tanmaylad77/KDT_Hierarchical_KiBot/HTML/images/cat_pdf_drill_map_LE_BMS_A_V2-PTH_drill_map.png

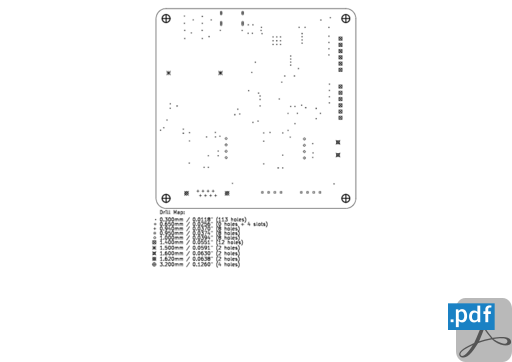
HTML/images/cat_pdf_drill_map_LE_BMS_A_V2-PTH_drill_map.png
