tanmaylad77/KDT_Hierarchical_KiBot/HTML/images/cat_png_3d_viewer_angled_bottom_LE_BMS_A_V2-angled_bottom.png

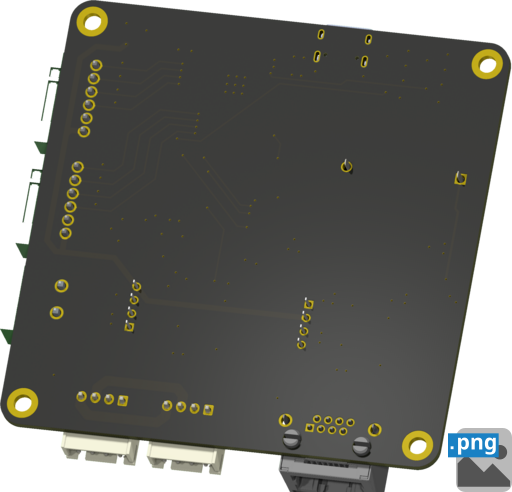
HTML/images/cat_png_3d_viewer_angled_bottom_LE_BMS_A_V2-angled_bottom.png
