tanmaylad77/KDT_Hierarchical_KiBot/Manufacturing/Fabrication/LE_BMS_A_V2-fabrication.pdf

# Top Fabrication (Scale 1:1)

# LE_BMS_A_V2 Fabrication Document

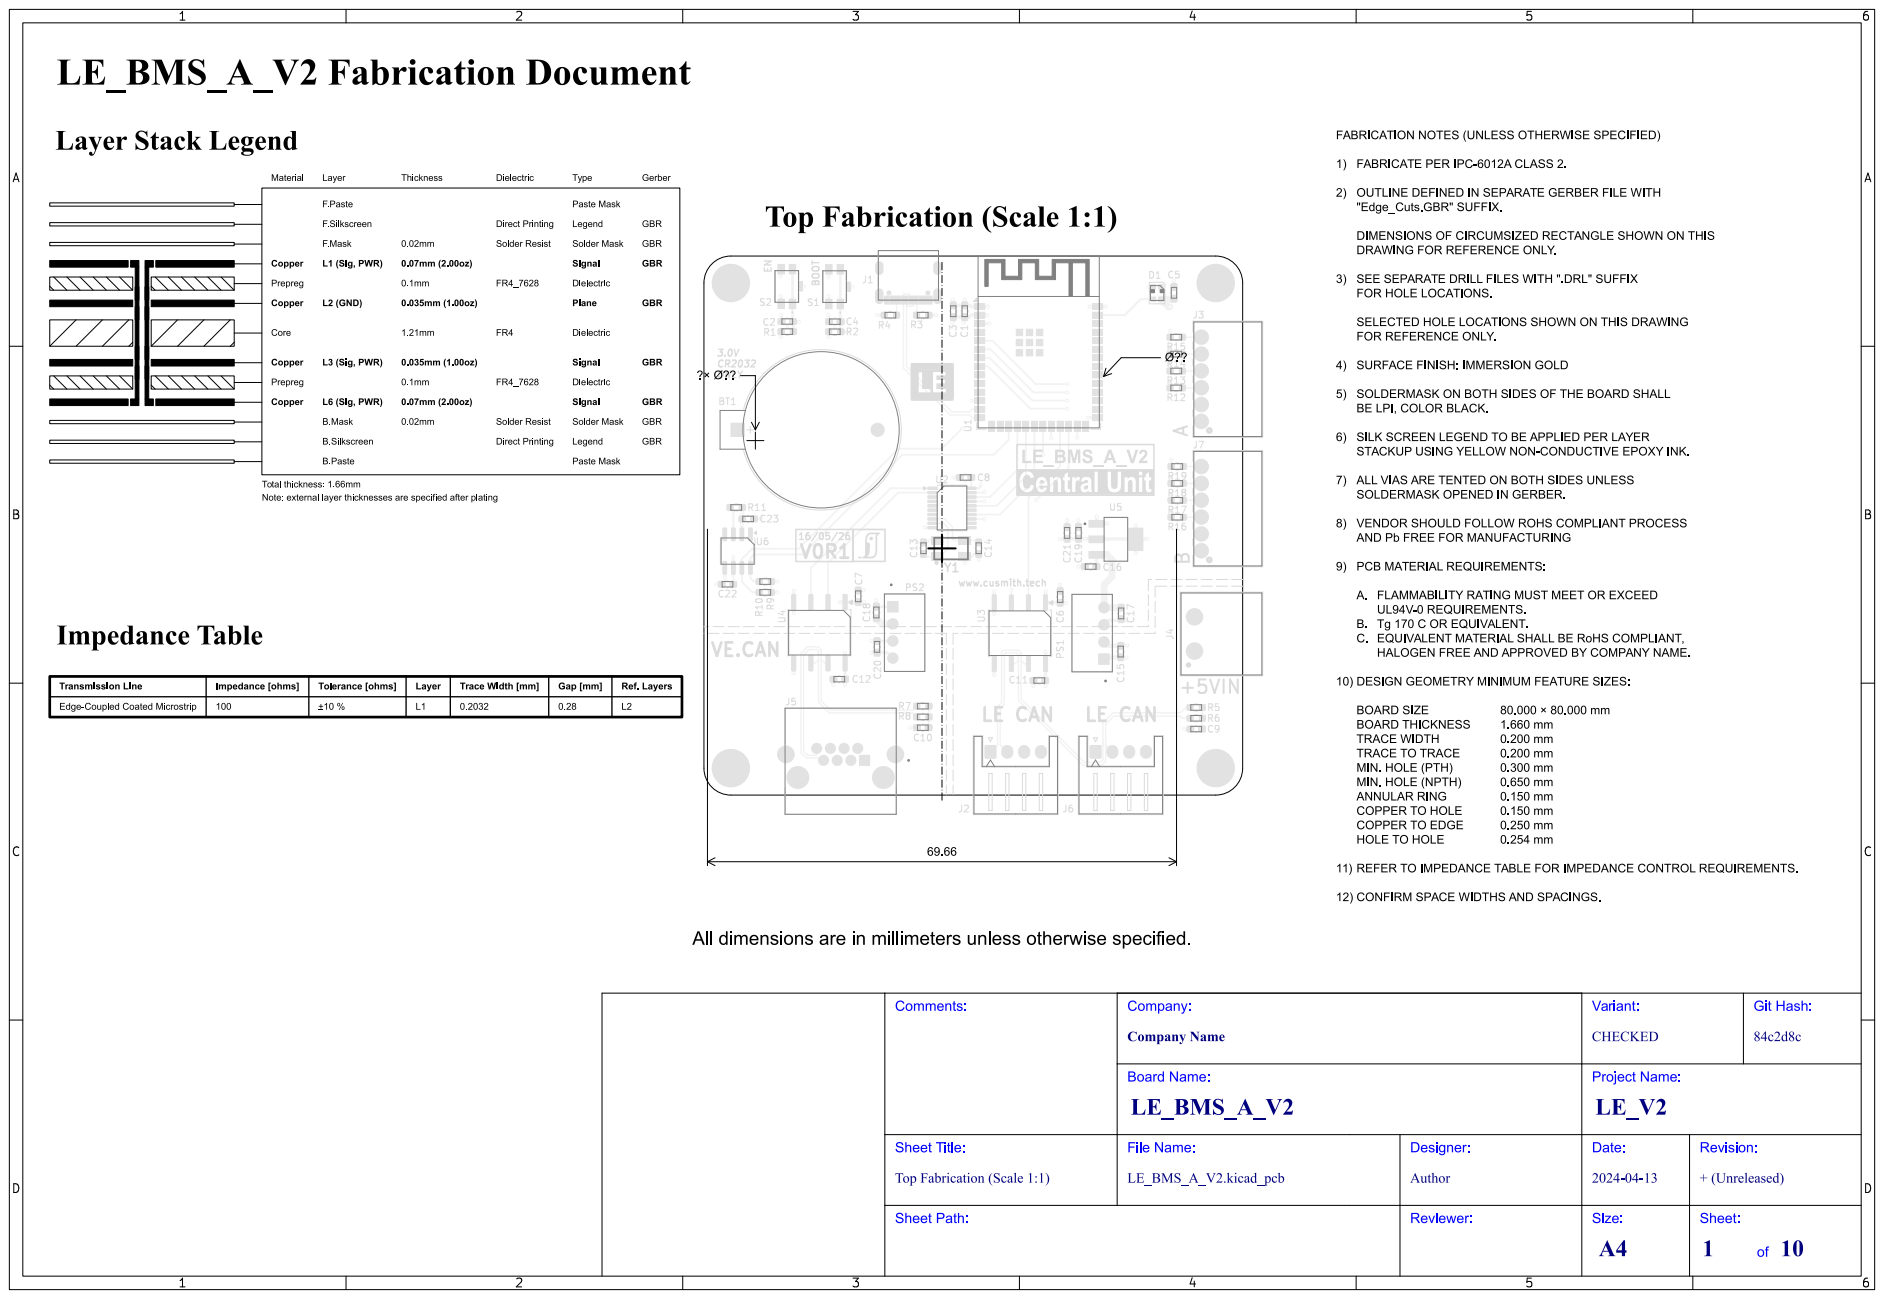
[picture p19: page 1]

# Bottom Fabrication (Scale 1:1)

# LE_BMS_A_V2 Fabrication Document

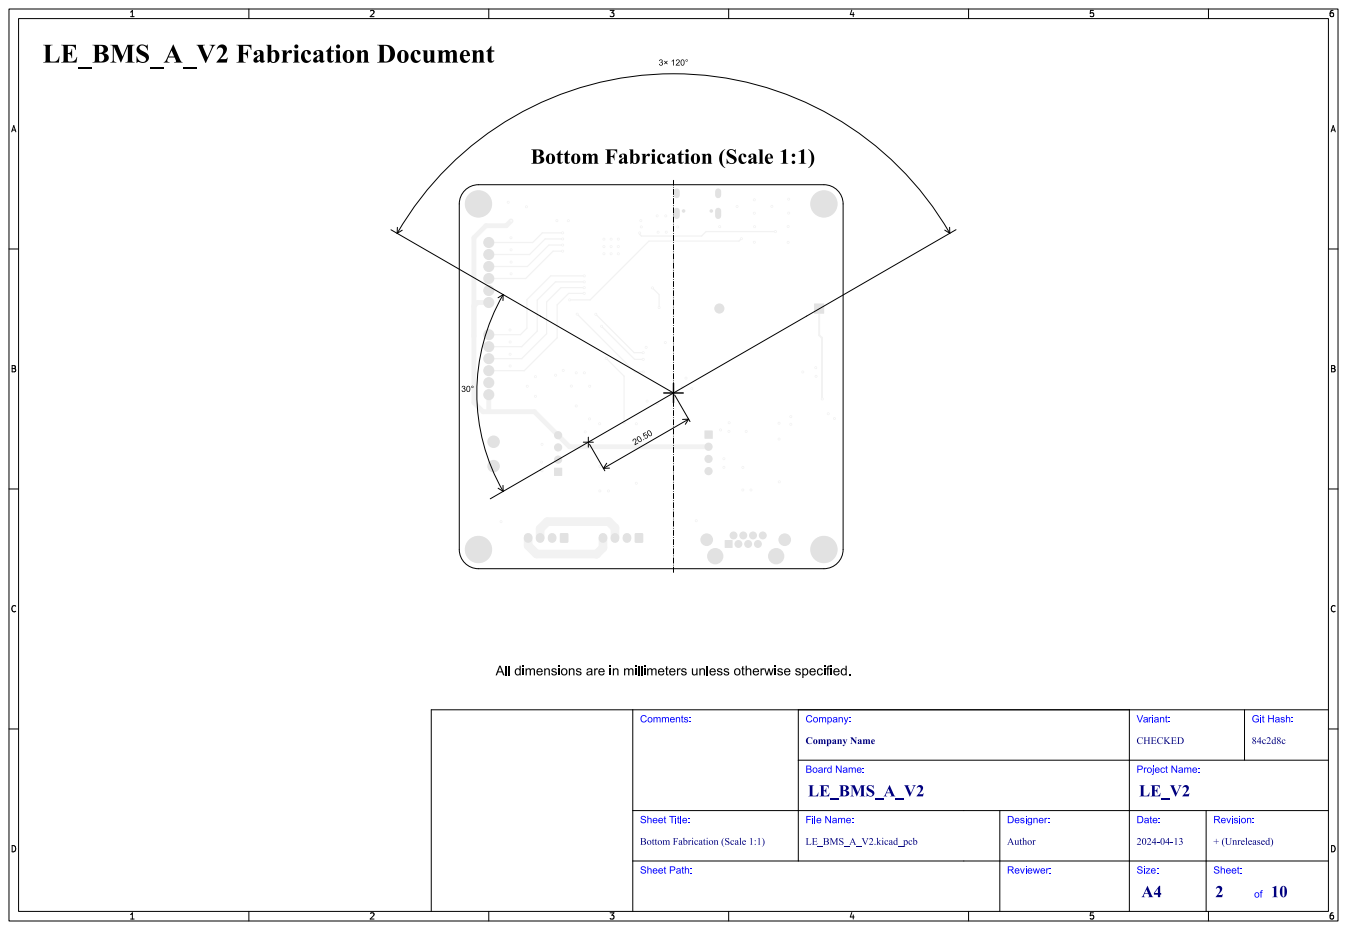
[picture p20: page 2]
Git; Hash:; Comments:; Sheet Path:; Sheet Title:; File Name:; LE_BMS_A_V2; Company Name; Company:; CHECKED; Variant:; Board Name:; LE_BMS_A_V2.kicad_pcb; Author; Designer:; Reviewer:; Project Name:; Date:; + (Unreleased); Revision:; Size:; Sheet:

Bottom Fabrication (Scale 1:1)

# Drill Drawing L1 - L4 (Scale 1:1)

# LE_BMS_A_V2 Fabrication Document

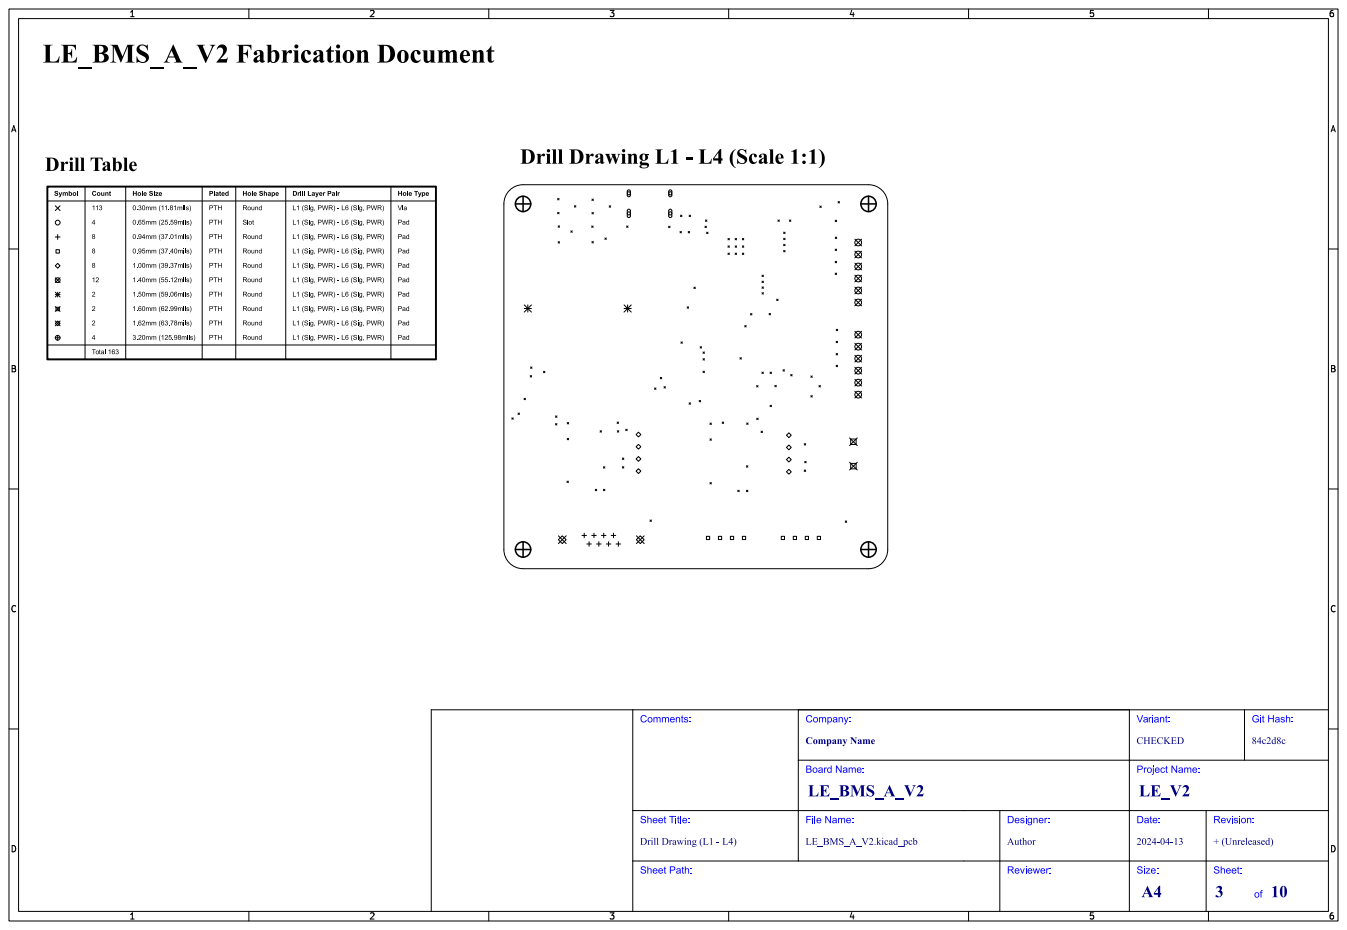
[picture p21: page 3]
Git; Hash:; Comments:; Drill Drawing (L1 - L4); Sheet Path:; Sheet Title:; File Name:; LE_BMS_A_V2; Company Name; Company:; CHECKED; Variant:; Board Name:; LE_BMS_A_V2.kicad_pcb; Author; Designer:; Reviewer:; Project Name:; Date:; + (Unreleased); Revision:; Size:; Sheet:

# Drill Drawing L1 - L4 (Scale 1:1)

# LE_BMS_A_V2 Fabrication Document

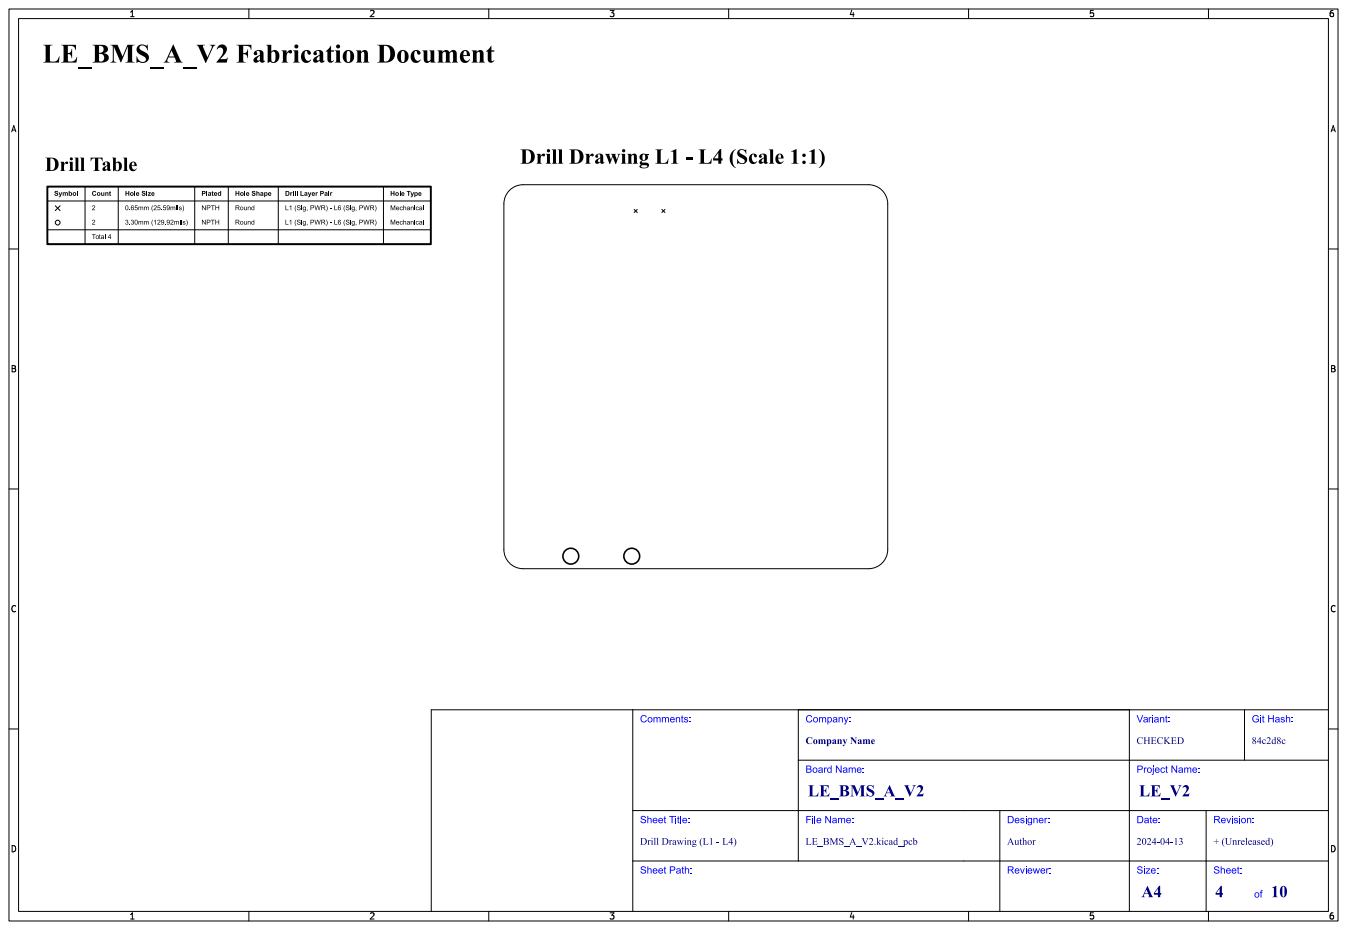
[picture p22: page 4]
Git; Hash:; Comments:; Drill Drawing (L1 - L4); Sheet Path:; Sheet Title:; File Name:; LE_BMS_A_V2; Company Name; Company:; CHECKED; Variant:; Board Name:; LE_BMS_A_V2.kicad_pcb; Author; Designer:; Reviewer:; Project Name:; Date:; + (Unreleased); Revision:; Size:; Sheet:

# Top Test Points (Scale 1:1)

# LE_BMS_A_V2 Fabrication Document

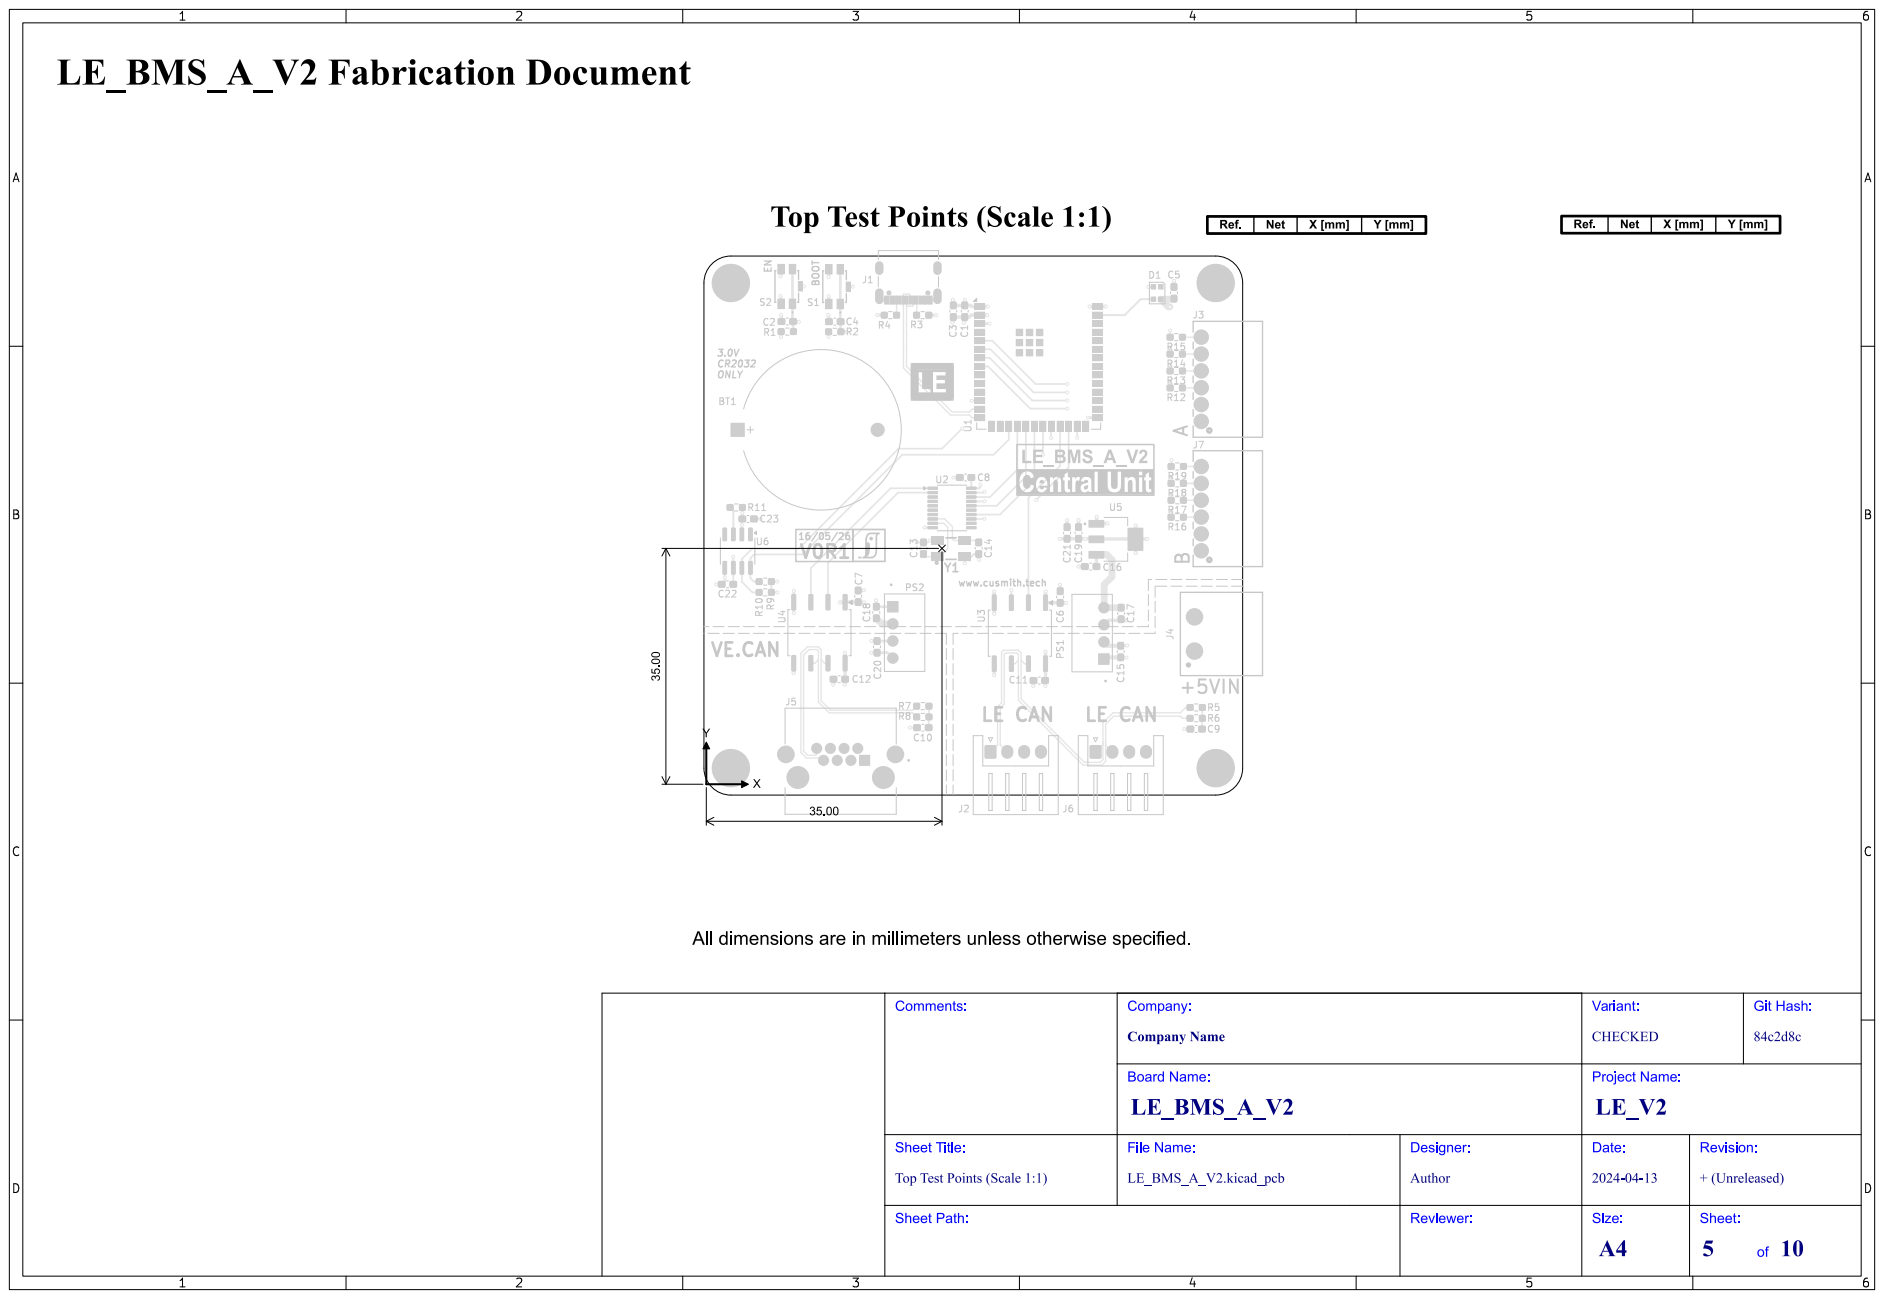
[picture p23: page 5]

Top Test Points (Scale 1:1)

# Bottom Test Points (Scale 1:1)

# LE_BMS_A_V2 Fabrication Document

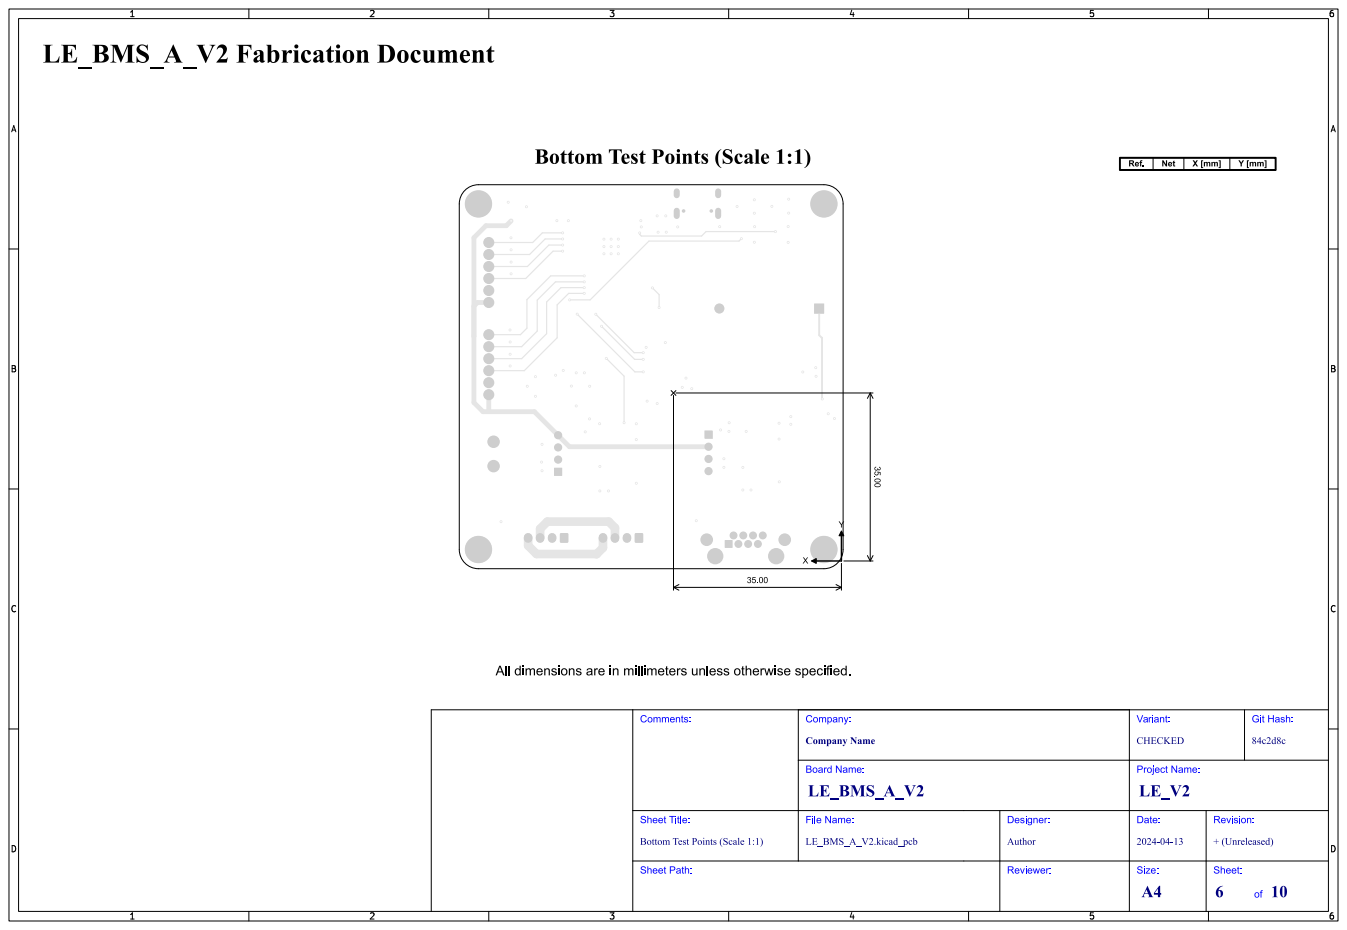
[picture p24: page 6]
Git; Hash:; Comments:; Sheet Path:; Sheet Title:; File Name:; LE_BMS_A_V2; Company Name; Company:; CHECKED; Variant:; Board Name:; LE_BMS_A_V2.kicad_pcb; Author; Designer:; Reviewer:; Project Name:; Date:; + (Unreleased); Revision:; Size:; Sheet:

Bottom Test Points (Scale 1:1)

# L1 (Sig, PWR) (Scale 1:1)

# LE_BMS_A_V2 Fabrication Document

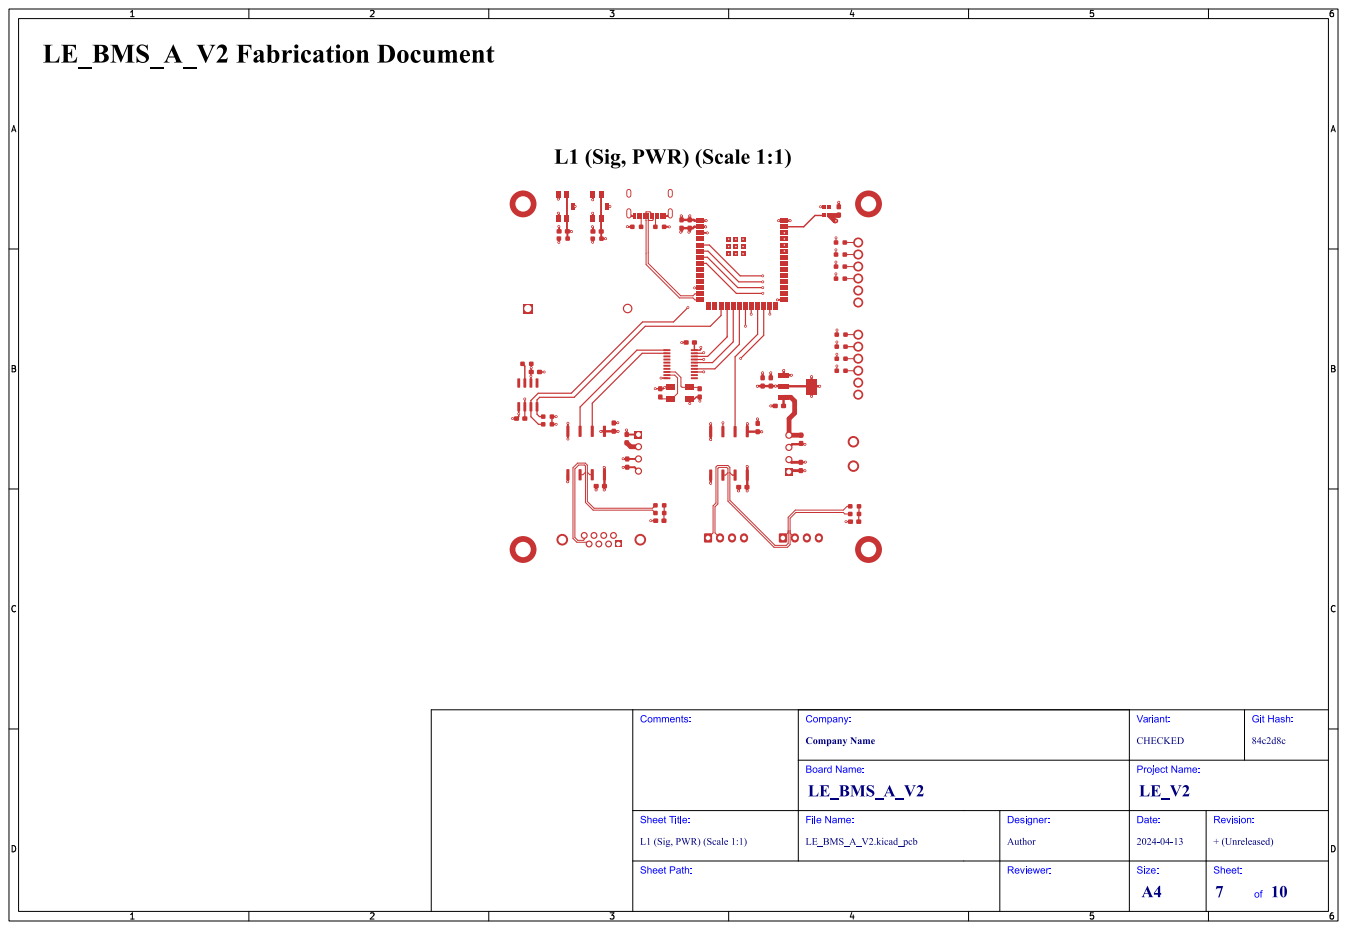
[picture p25: page 7]
Git; Hash:; Comments:; Sheet Path:; Sheet Title:; File Name:; LE_BMS_A_V2; Company Name; Company:; CHECKED; Variant:; Board Name:; LE_BMS_A_V2.kicad_pcb; Author; Designer:; Reviewer:; Project Name:; Date:; + (Unreleased); Revision:; Size:; Sheet:

L1 (Sig, PWR) (Scale 1:1)

# L2 (GND) (Scale 1:1)

# LE_BMS_A_V2 Fabrication Document

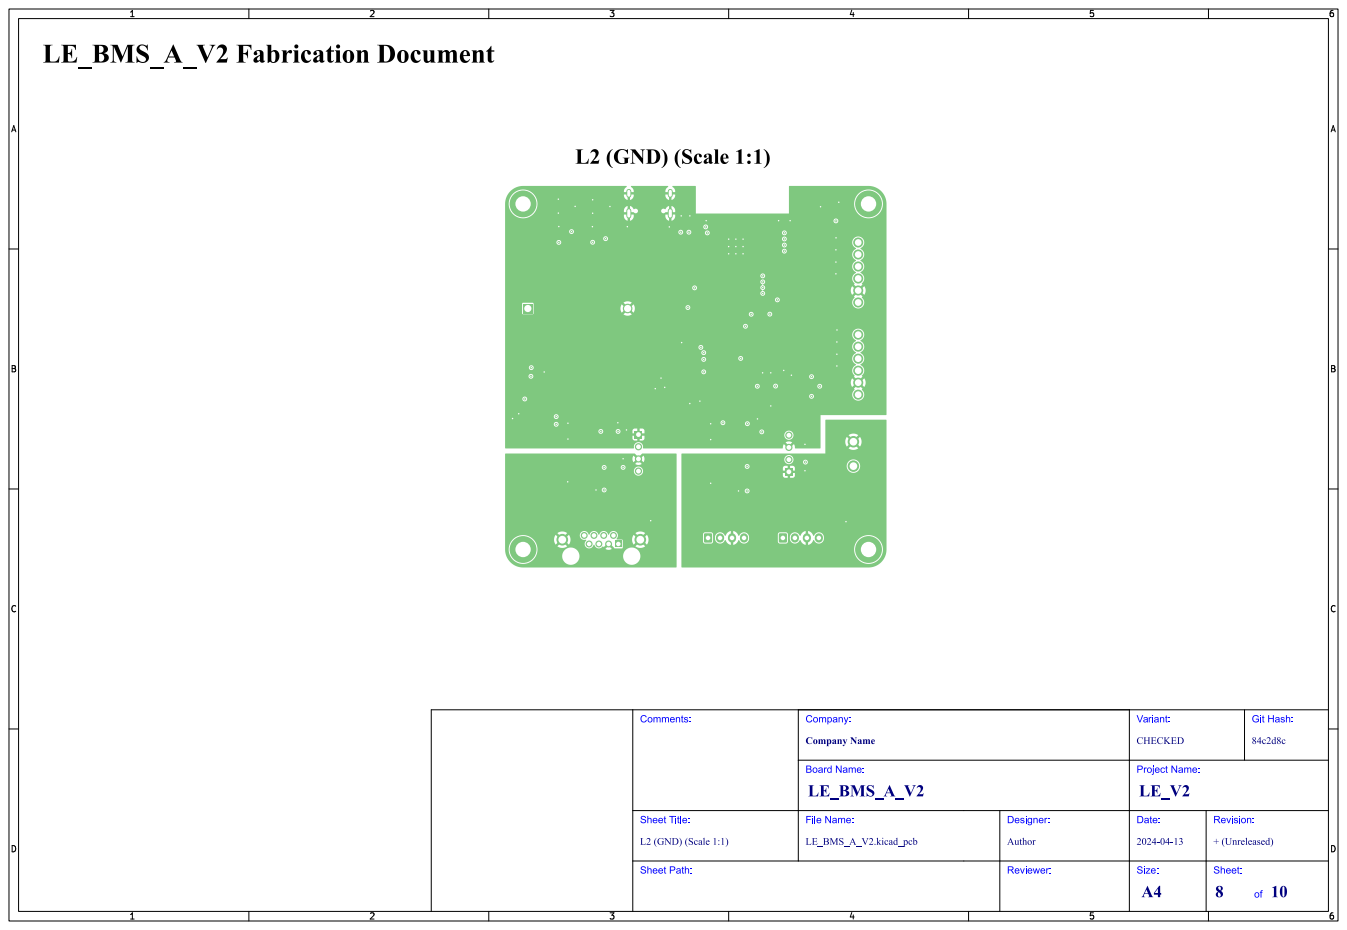
[picture p26: page 8]
Git; Hash:; Comments:; L2 (GND) (Scale 1:1); Sheet Path:; Sheet Title:; File Name:; LE_BMS_A_V2; Company Name; Company:; CHECKED; Variant:; Board Name:; LE_BMS_A_V2.kicad_pcb; Author; Designer:; Reviewer:; Project Name:; Date:; + (Unreleased); Revision:; Size:; Sheet:

# L3 (Sig, PWR) (Scale 1:1)

# LE_BMS_A_V2 Fabrication Document

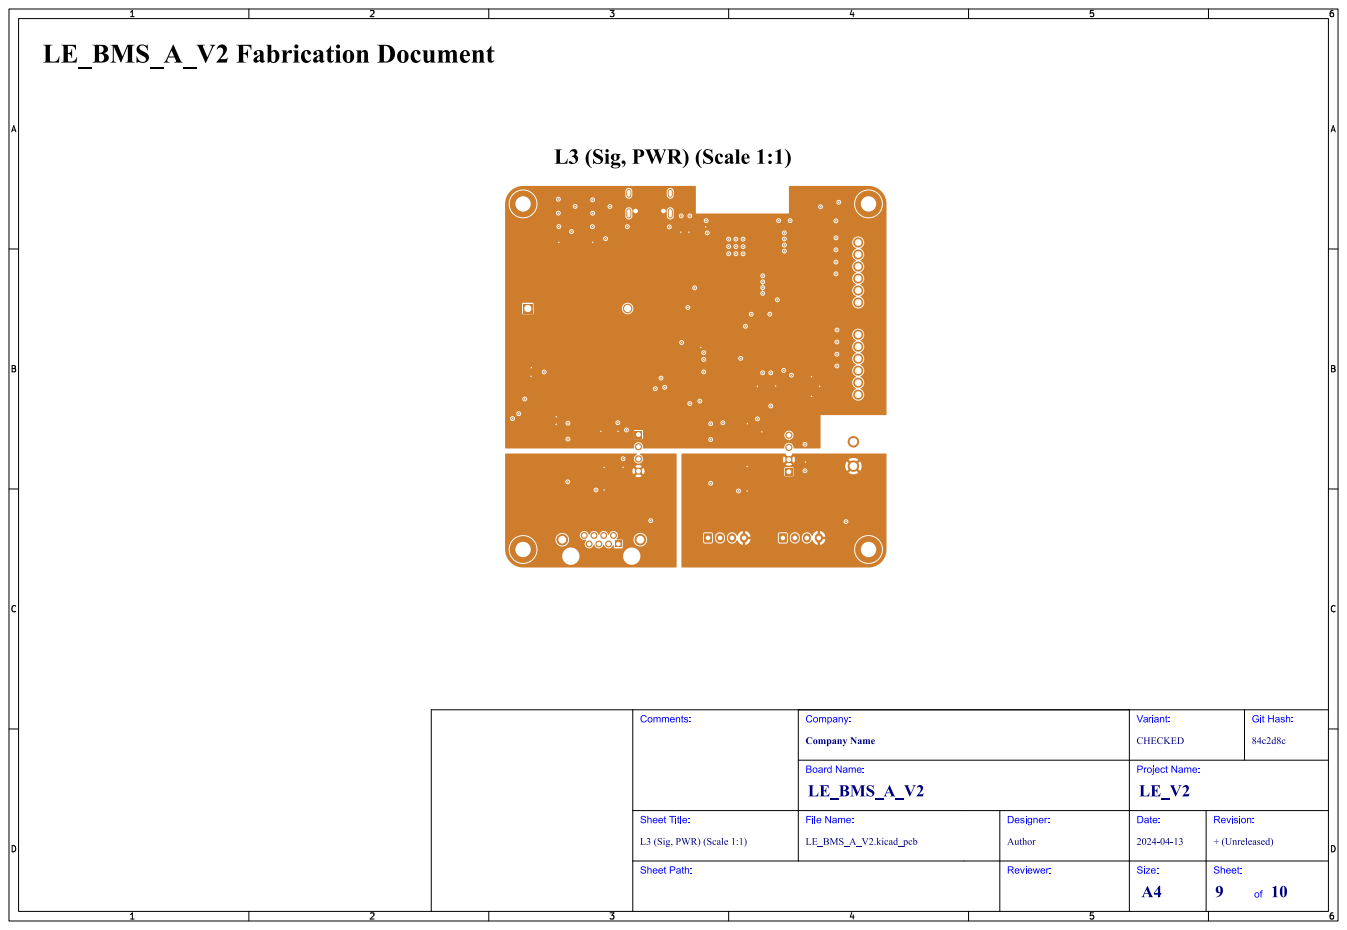
[picture p27: page 9]
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

L3 (Sig, PWR) (Scale 1:1)

# L6 (Sig, PWR) (Scale 1:1)

# LE_BMS_A_V2 Fabrication Document

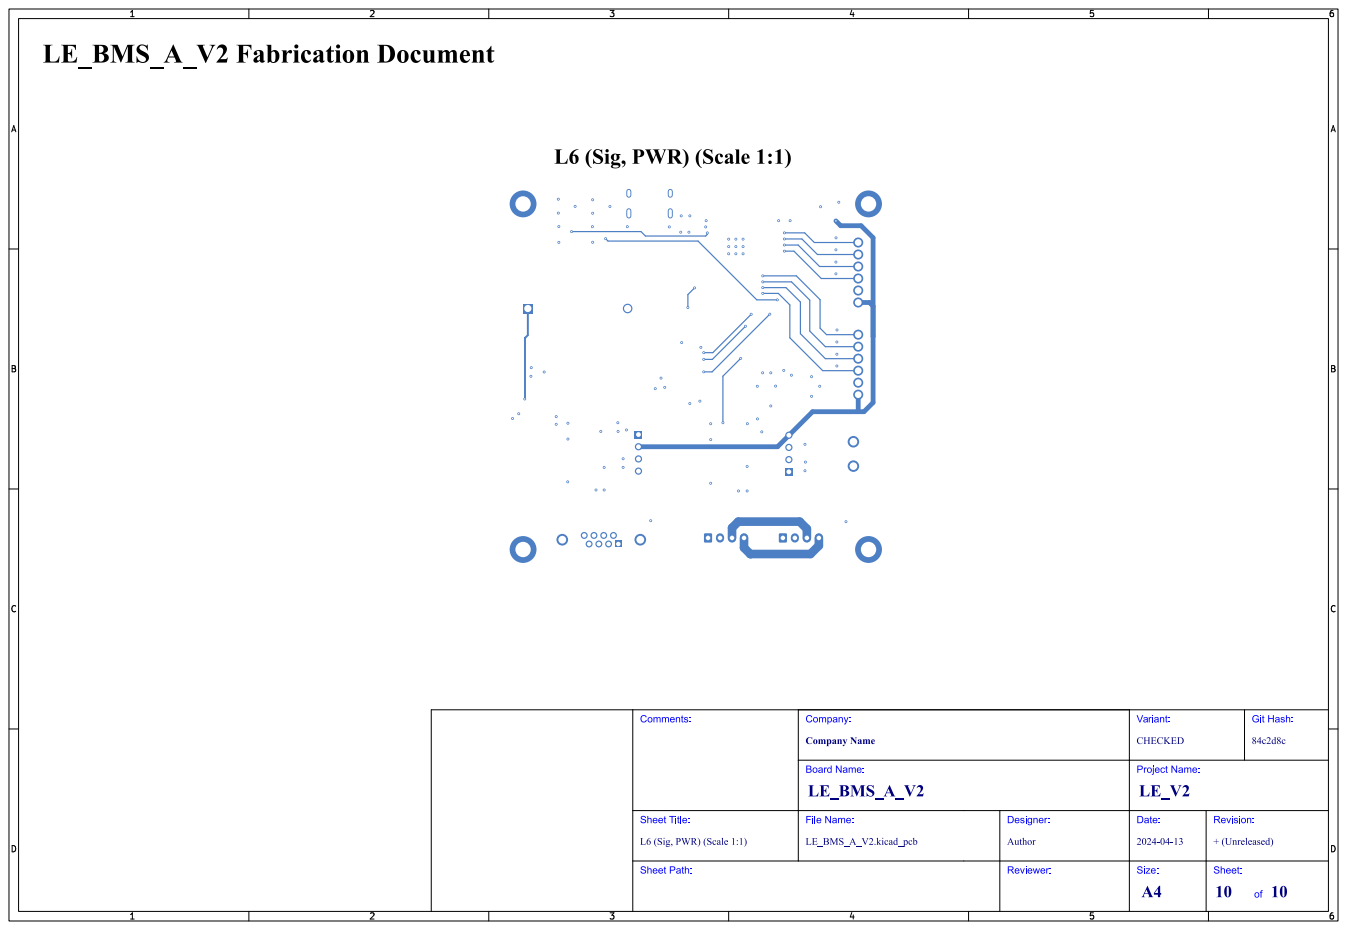
[picture p28: page 10]
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

L6 (Sig, PWR) (Scale 1:1)
