tanmaylad77/KDT_Hierarchical_KiBot/Manufacturing/Assembly/LE_BMS_A_V2-assembly-3.pdf

# Bottom Assembly (Scale 1:1)

# LE_BMS_A_V2 Assembly Document

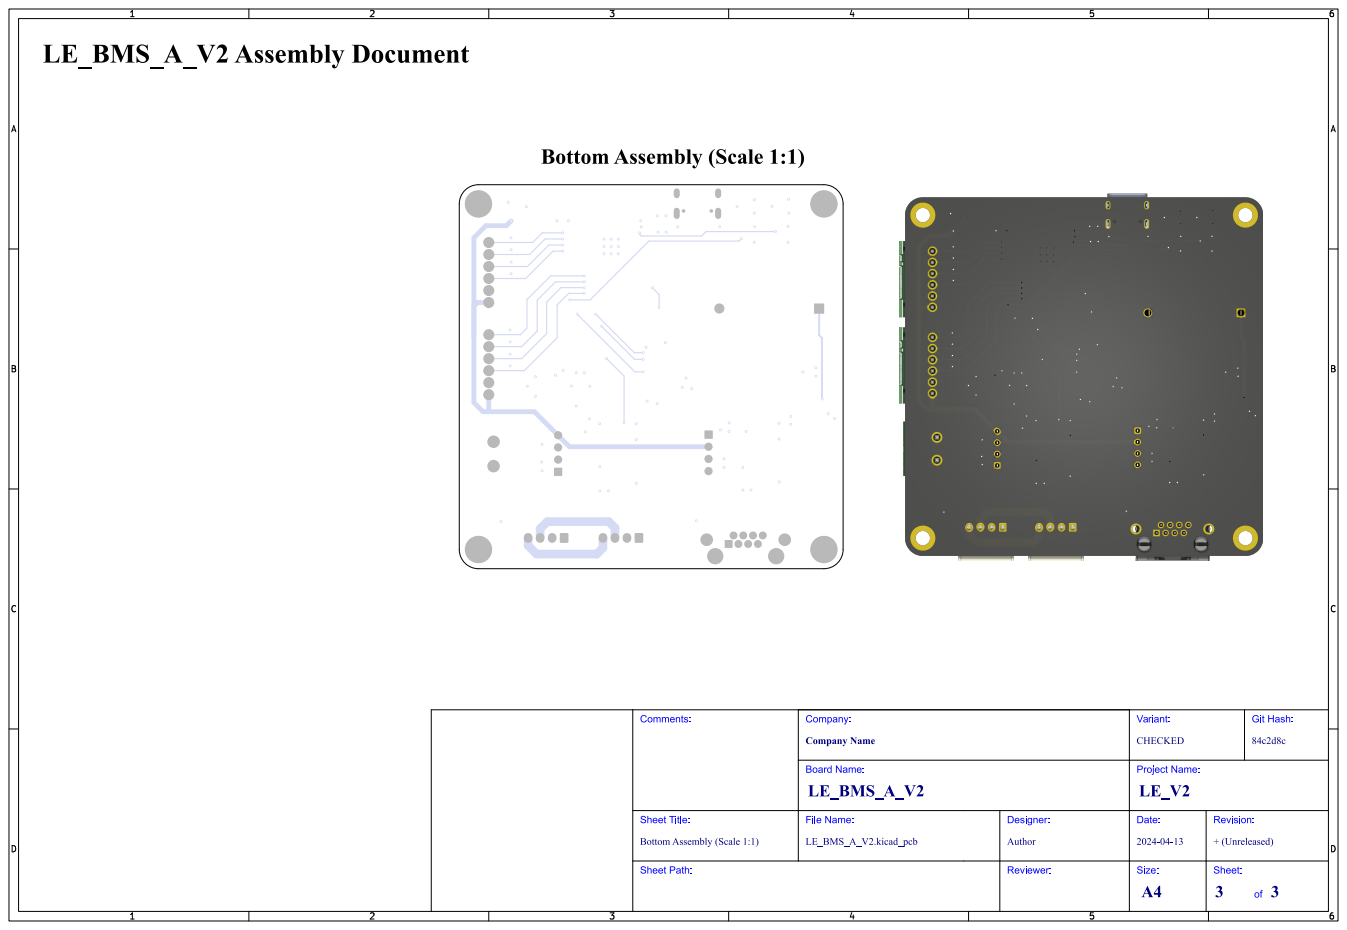
[picture p41: page 1]
Git; Hash:; Comments:; Sheet Path:; Sheet Title:; File Name:; LE_BMS_A_V2; Company Name; Company:; CHECKED; Variant:; Board Name:; LE_BMS_A_V2.kicad_pcb; Author; Designer:; Reviewer:; Project Name:; Date:; + (Unreleased); Revision:; Size:; Sheet: 3

Bottom Assembly (Scale 1:1)
