tanmaylad77/KDT_Hierarchical_KiBot/Manufacturing/Assembly/LE_BMS_A_V2-assembly.pdf

# LE_BMS_A_V2 Assembly Document

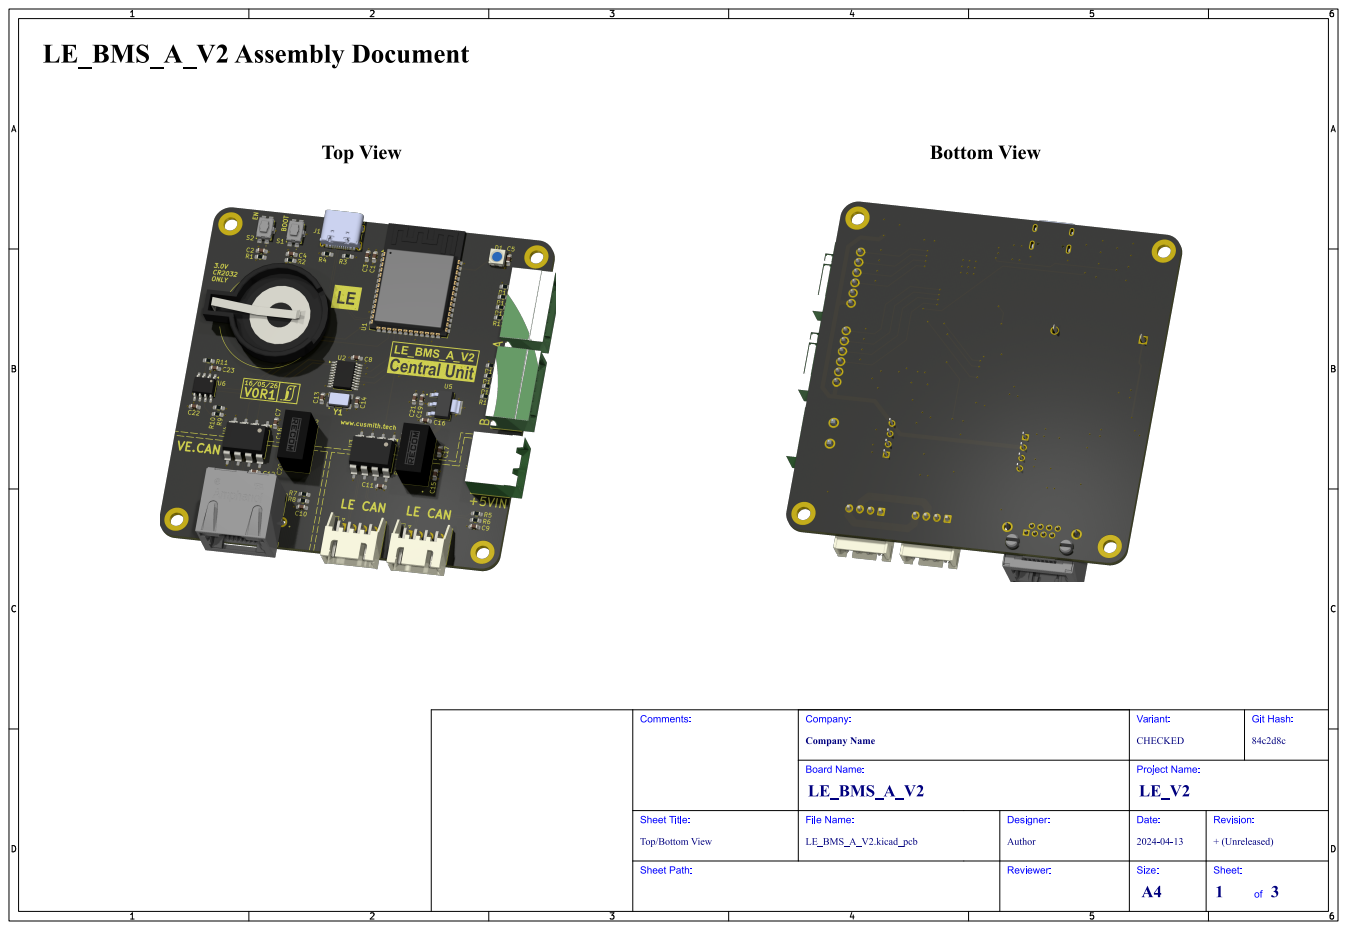
[picture p42: page 1]
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

Top/Bottom View

# Top Assembly (Scale 1:1)

# LE_BMS_A_V2 Assembly Document


# Bottom Assembly (Scale 1:1)

# LE_BMS_A_V2 Assembly Document

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

Bottom Assembly (Scale 1:1)
