tanmaylad77/KDT_Hierarchical_KiBot/Manufacturing/Fabrication/LE_BMS_A_V2-fabrication-10.pdf

# L6 (Sig, PWR) (Scale 1:1)

# LE_BMS_A_V2 Fabrication Document

Git; Hash:; Comments:; Sheet Path:; Sheet Title:; File Name:; LE_BMS_A_V2; Company Name; Company:; CHECKED; Variant:; Board Name:; LE_BMS_A_V2.kicad_pcb; Author; Designer:; Reviewer:; Project Name:; Date:; + (Unreleased); Revision:; Size:; Sheet: 10

L6 (Sig, PWR) (Scale 1:1)
