tanmaylad77/KDT_Hierarchical_KiBot/Manufacturing/Fabrication/LE_BMS_A_V2-fabrication-1.pdf

# Top Fabrication (Scale 1:1)

# LE_BMS_A_V2 Fabrication Document
