tanmaylad77/KDT_Hierarchical_KiBot/Manufacturing/Fabrication/LE_BMS_A_V2-fabrication-5.pdf

# Top Test Points (Scale 1:1)

# LE_BMS_A_V2 Fabrication Document


Top Test Points (Scale 1:1)
