tanmaylad77/KDT_Hierarchical_KiBot/Manufacturing/Fabrication/Gerbers/LE_BMS_A_V2-NPTH_drill_map.pdf

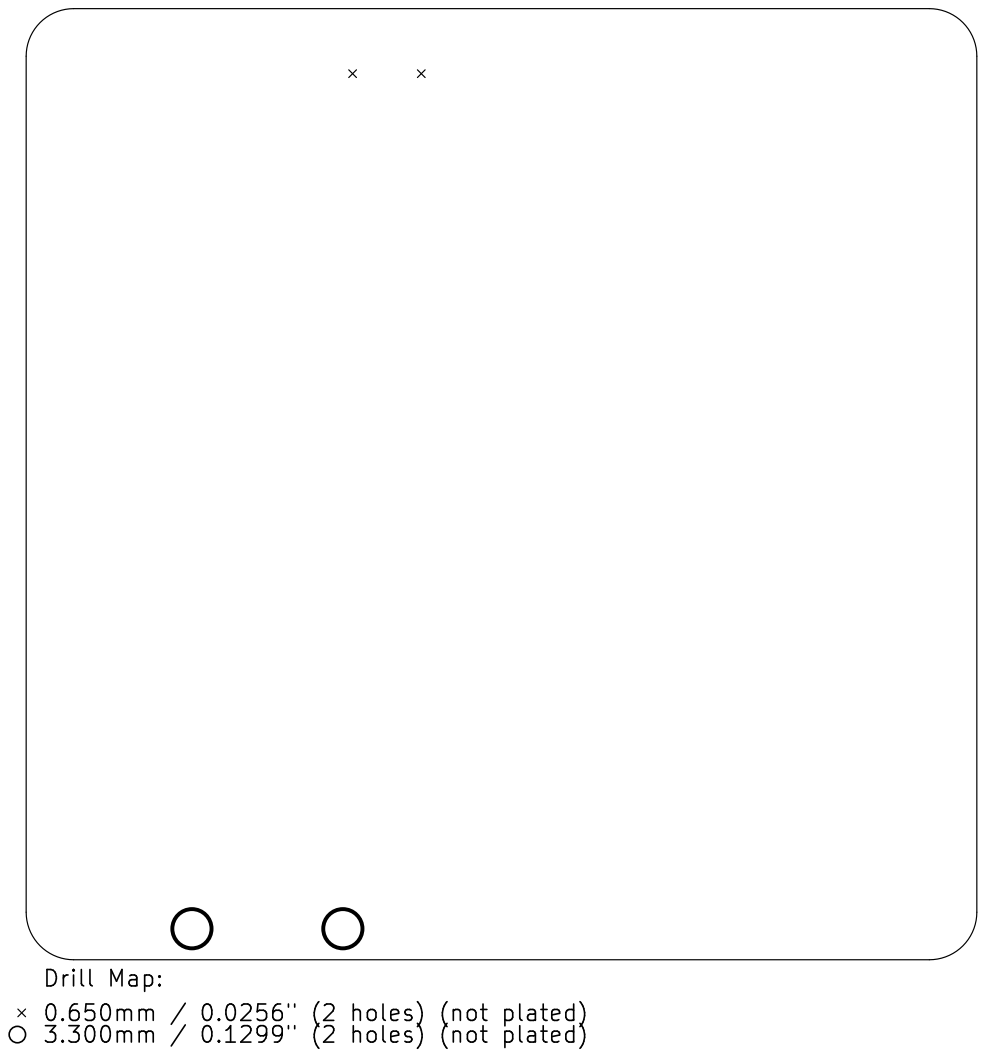
[picture p43: page 1]
