tanmaylad77/KDT_Hierarchical_KiBot/Manufacturing/Fabrication/Gerbers/LE_BMS_A_V2-PTH_drill_map.pdf

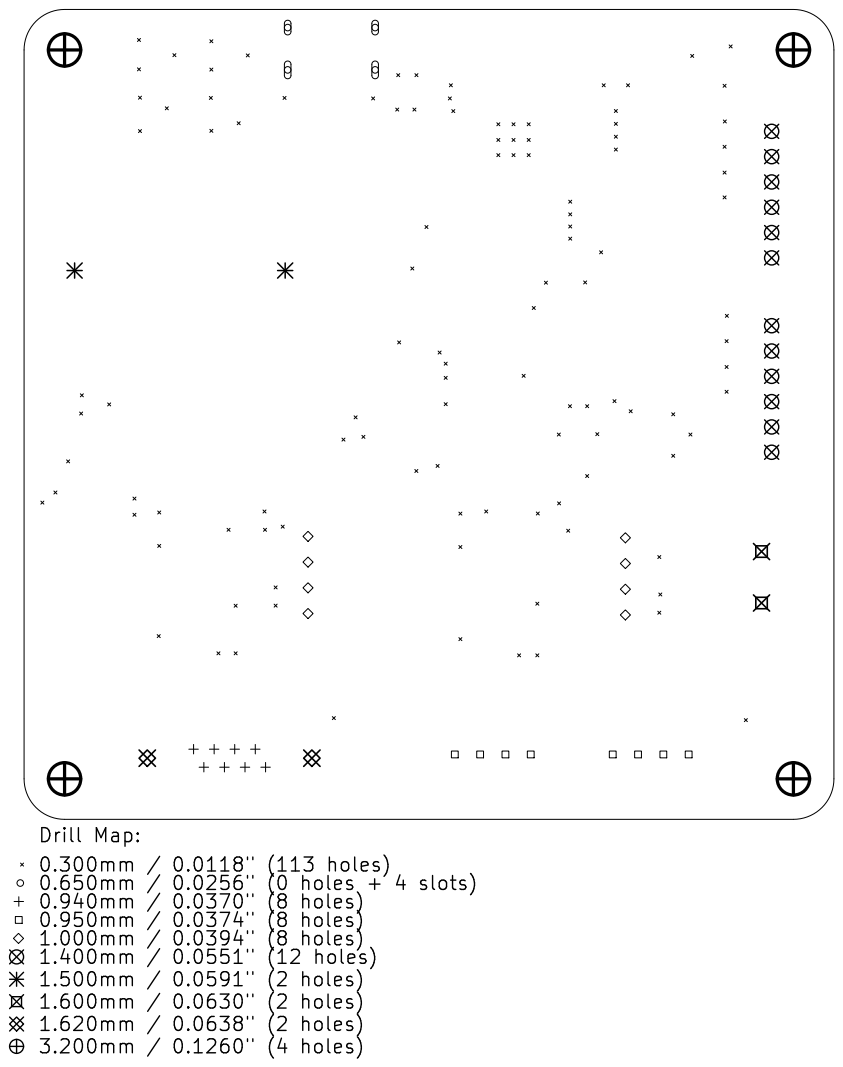
[picture p44: page 1]
